roccodm/undeRaspWater/Images/board/IMG_20170130_133051.jpg

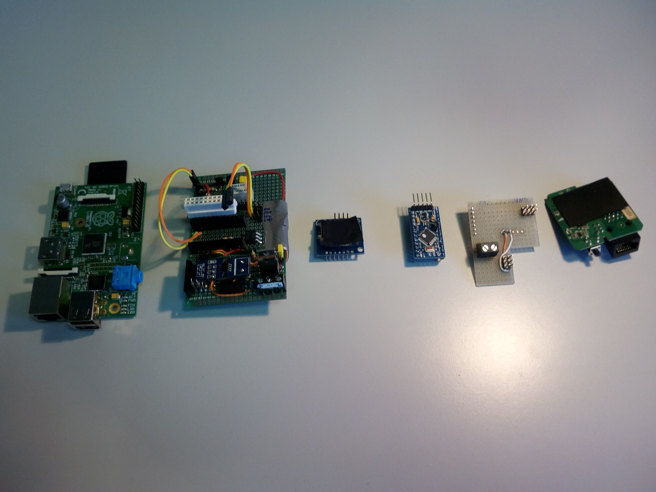
Images/board/IMG_20170130_133051.jpg
