roccodm/undeRaspWater/Images/board/IMG_20170130_133103.jpg

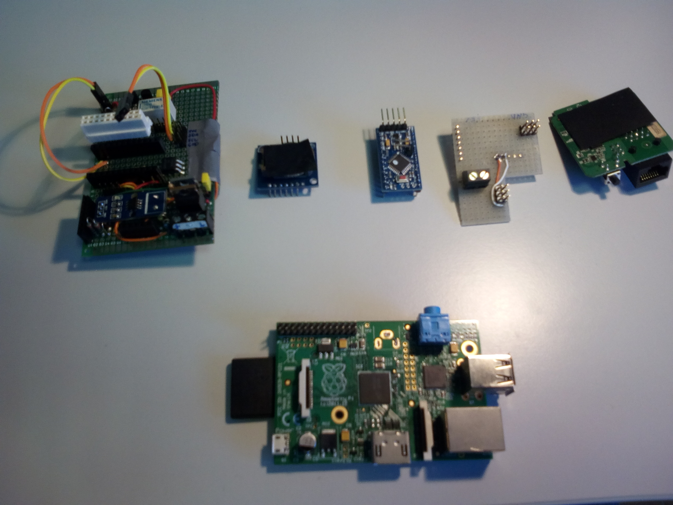
Images/board/IMG_20170130_133103.jpg
