roccodm/undeRaspWater/Images/board/IMG_20170130_133119.jpg

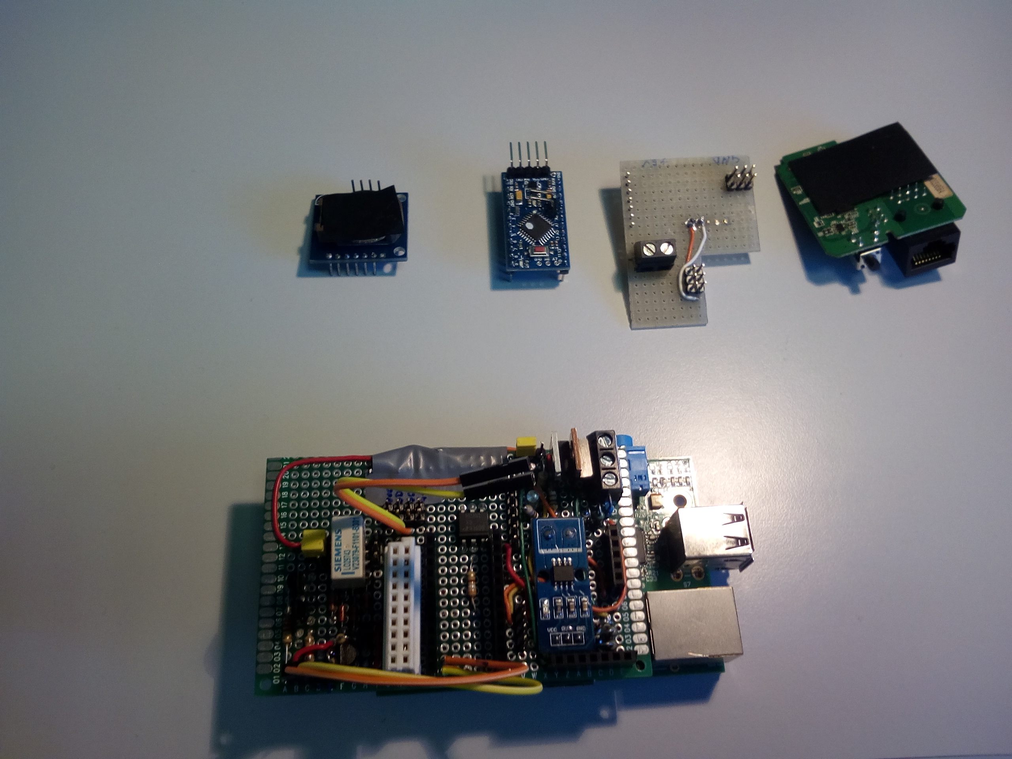
Images/board/IMG_20170130_133119.jpg
