roccodm/undeRaspWater/Images/board/IMG_20170130_133140.jpg

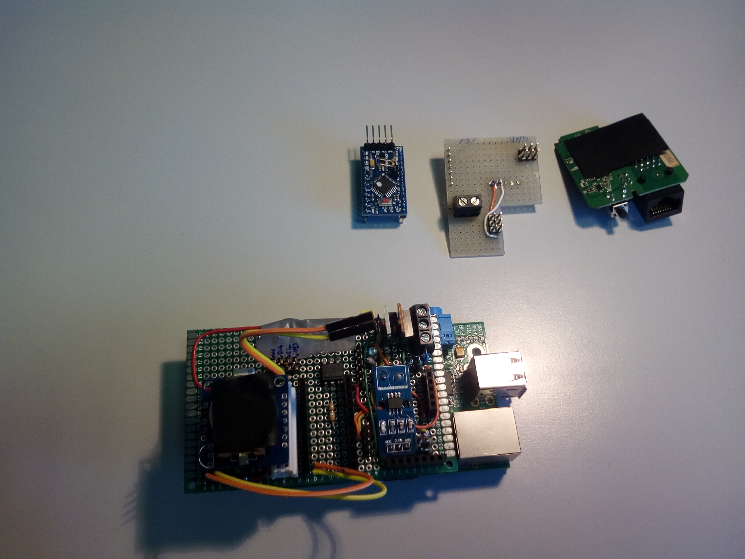
Images/board/IMG_20170130_133140.jpg
