roccodm/undeRaspWater/Images/board/IMG_20170130_133158.jpg

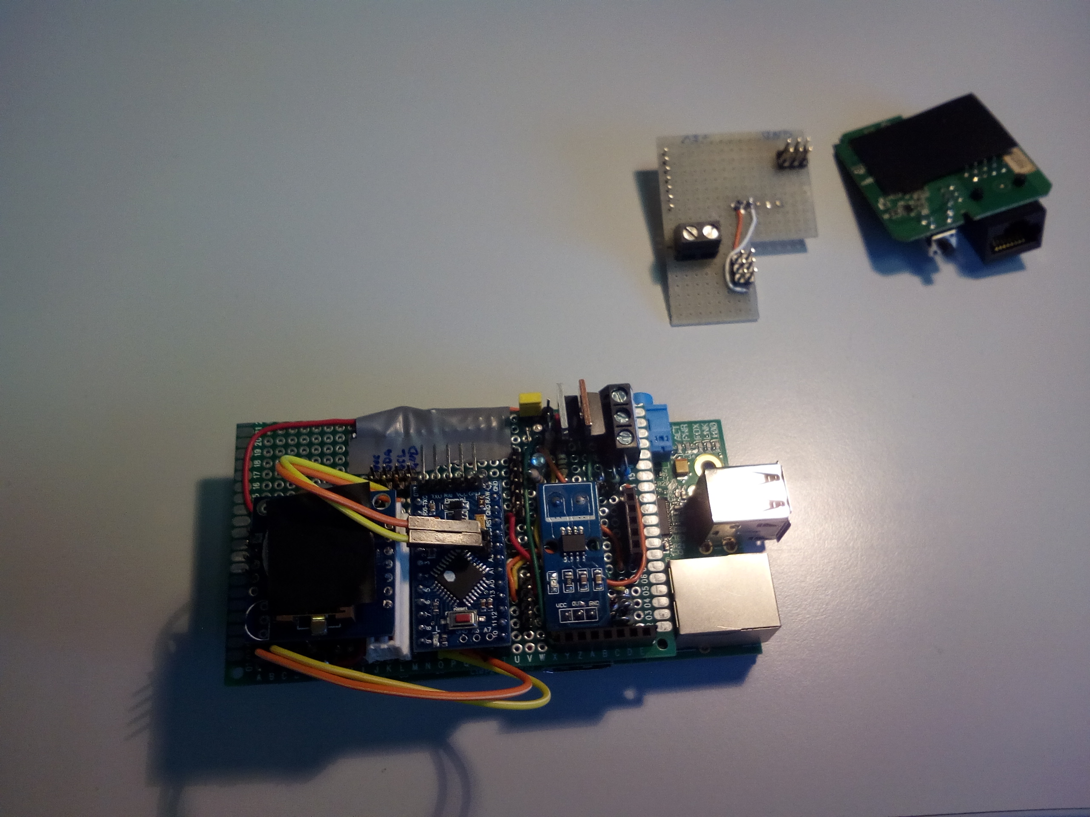
Images/board/IMG_20170130_133158.jpg
