roccodm/undeRaspWater/Images/board/IMG_20170130_133218.jpg

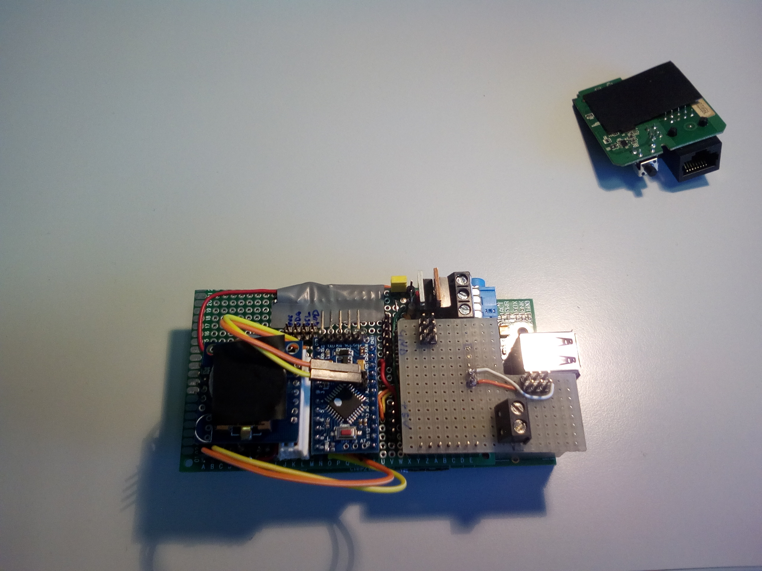
Images/board/IMG_20170130_133218.jpg
