roccodm/undeRaspWater/Images/board/IMG_20170130_133238.jpg

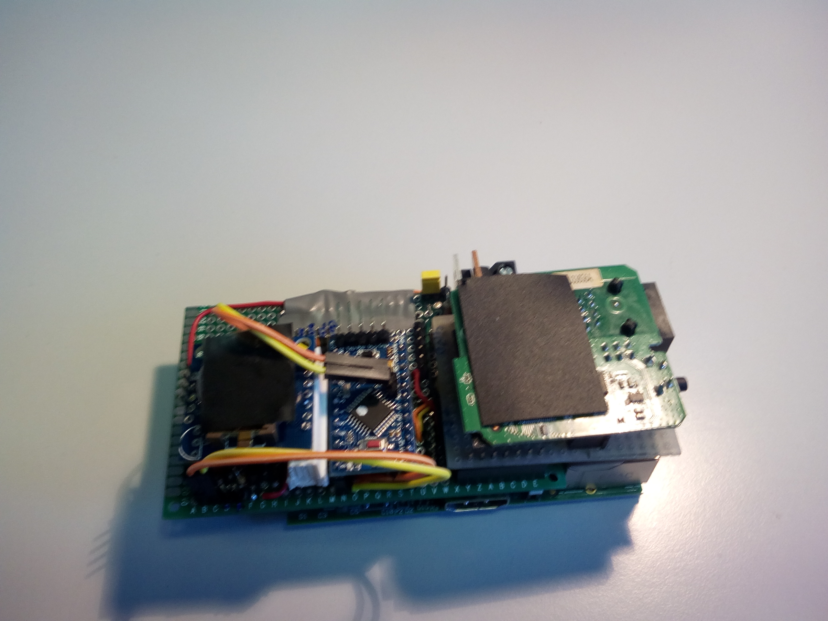
Images/board/IMG_20170130_133238.jpg
