roccodm/undeRaspWater/Images/board/IMG_20170130_133250.jpg

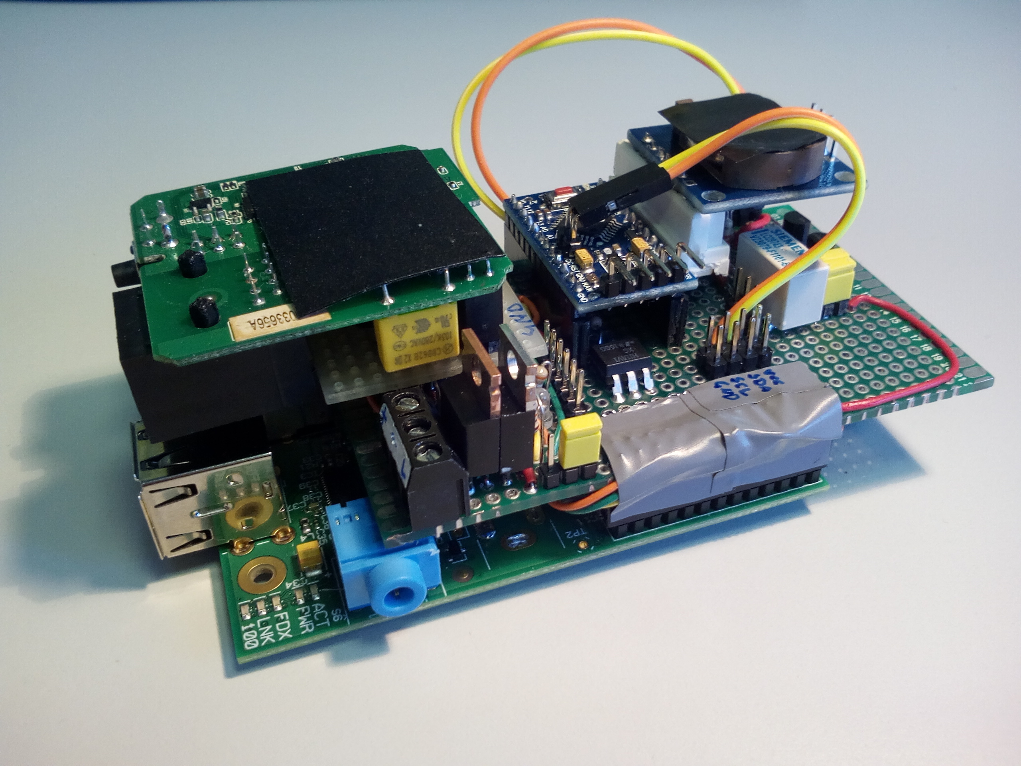
Images/board/IMG_20170130_133250.jpg
