roccodm/undeRaspWater/Images/board/IMG_20170202_100003.jpg

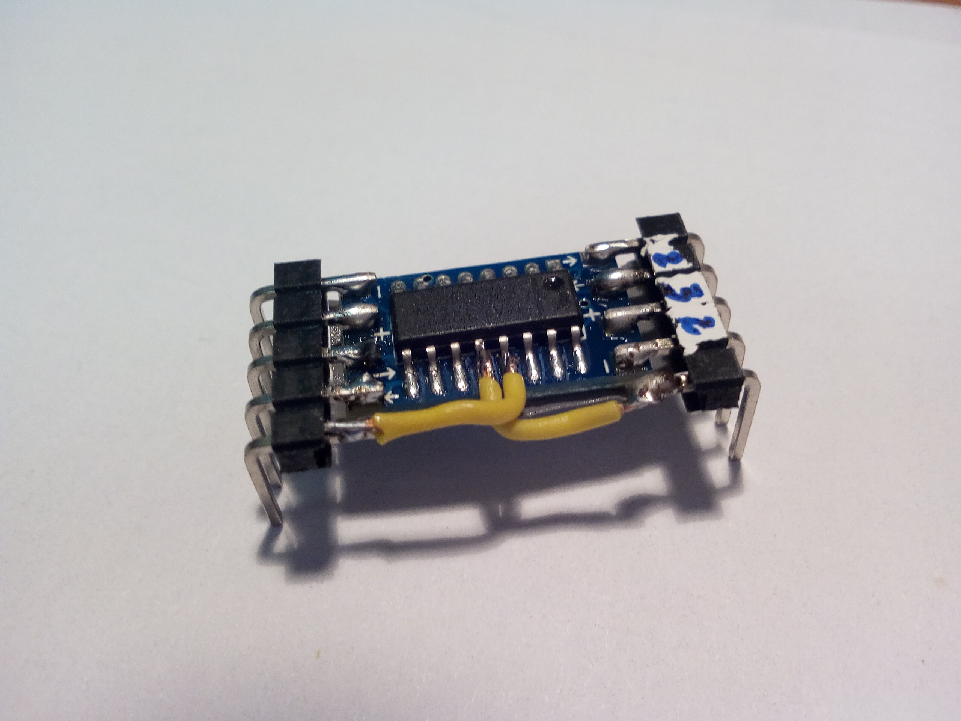
Images/board/IMG_20170202_100003.jpg
