roccodm/undeRaspWater/Images/board/IMG_20170202_102142.jpg

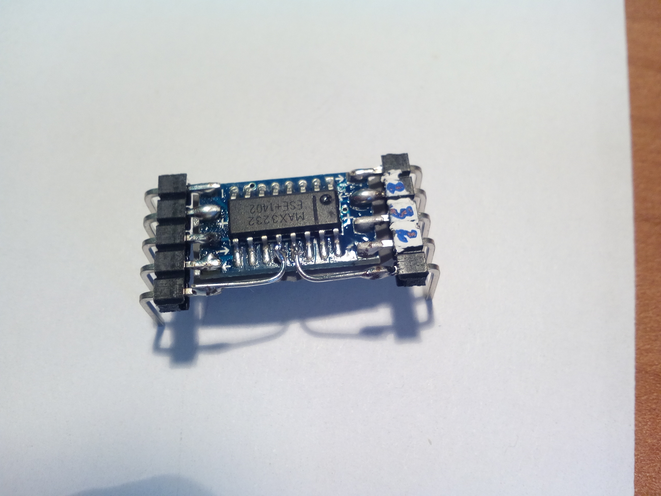
Images/board/IMG_20170202_102142.jpg
