roccodm/undeRaspWater/Images/board/IMG_20170202_103730.jpg

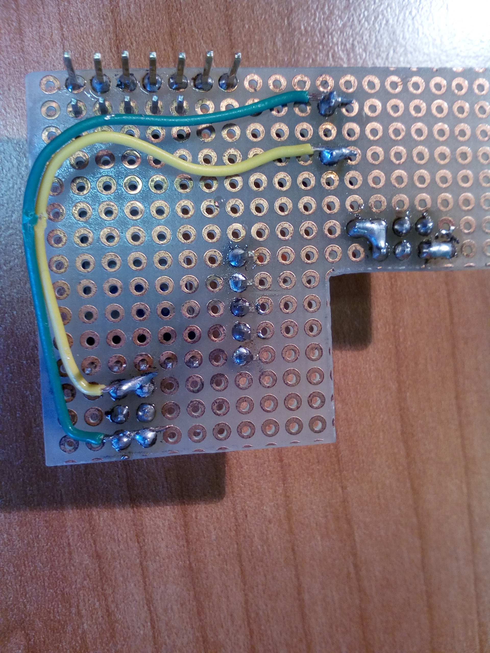
Images/board/IMG_20170202_103730.jpg
