roccodm/undeRaspWater/Images/board/IMG_20170202_123904.jpg

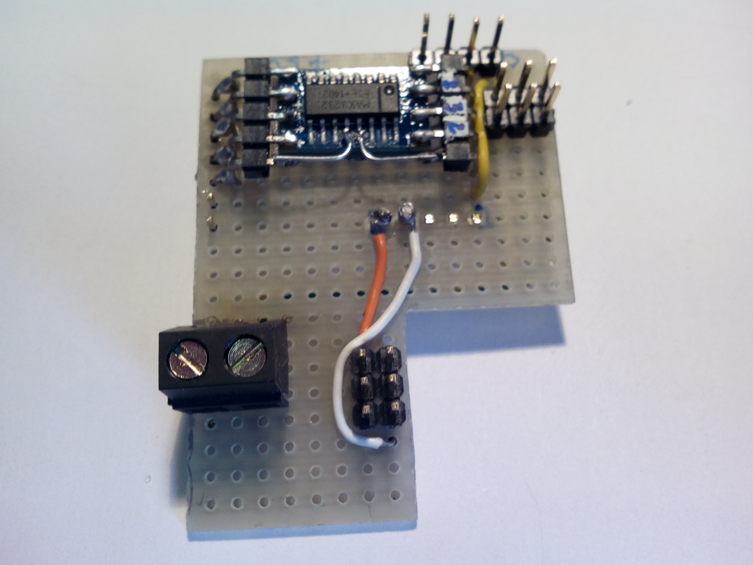
Images/board/IMG_20170202_123904.jpg
