roccodm/undeRaspWater/Images/board/IMG_20170202_125238.jpg

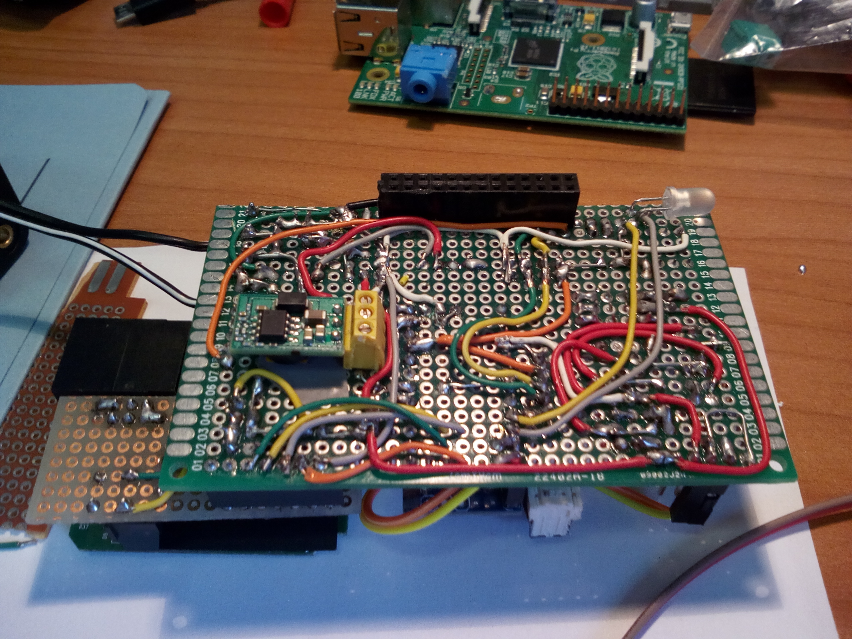
Images/board/IMG_20170202_125238.jpg
