roccodm/undeRaspWater/Images/board/IMG_20170202_125248.jpg

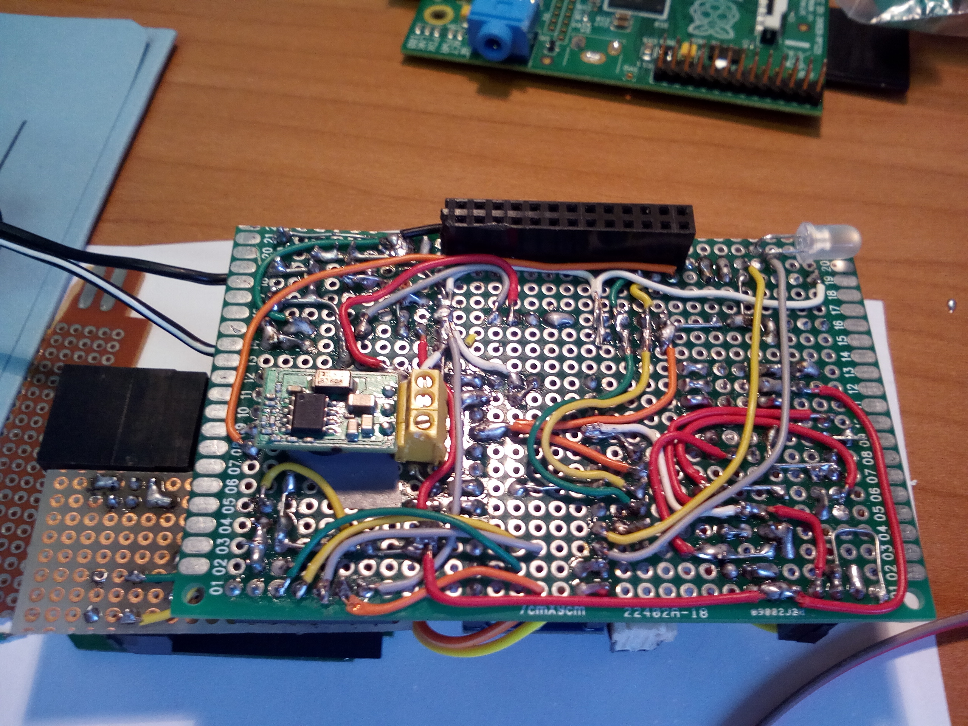
Images/board/IMG_20170202_125248.jpg
