roccodm/undeRaspWater/Images/board/IMG_20170202_141850.jpg

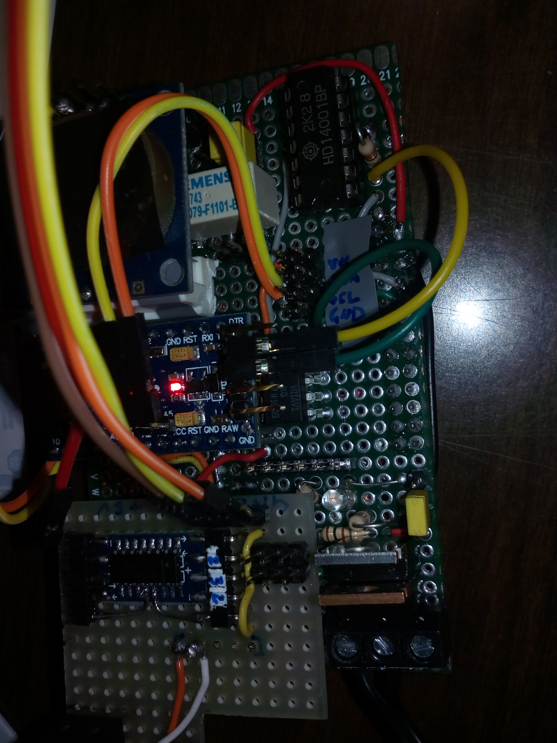
Images/board/IMG_20170202_141850.jpg
