roccodm/undeRaspWater/Images/board/IMG_20170203_102233.jpg

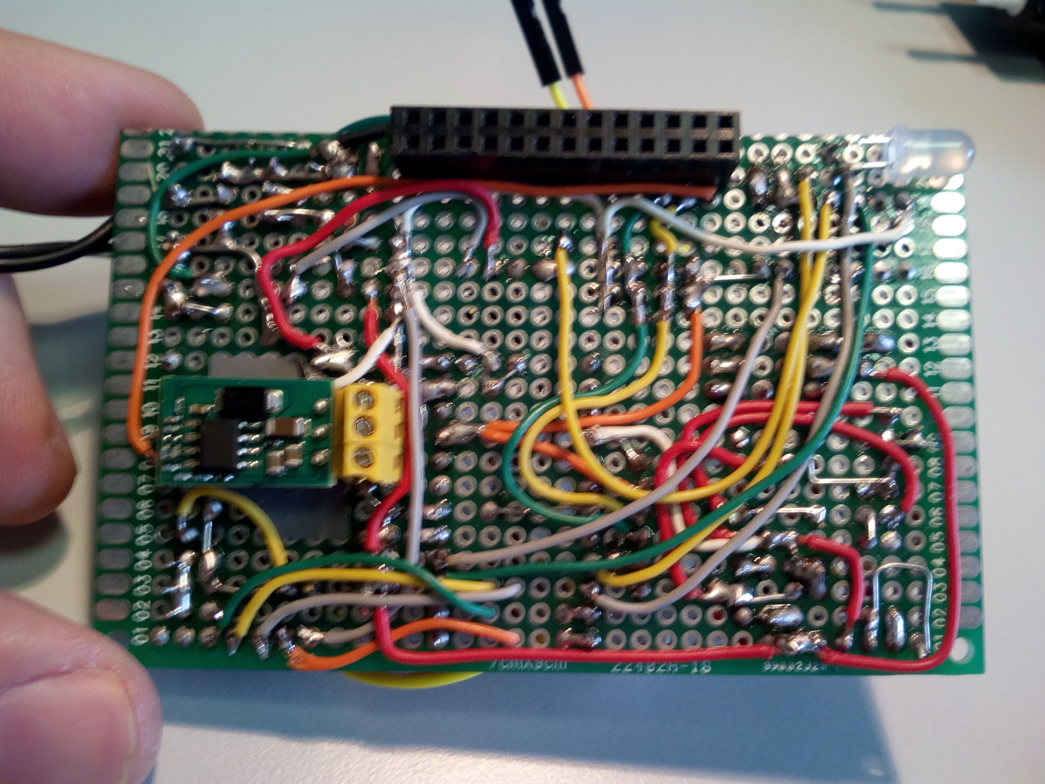
Images/board/IMG_20170203_102233.jpg
