roccodm/undeRaspWater/Images/board/IMG_20170203_102318.jpg

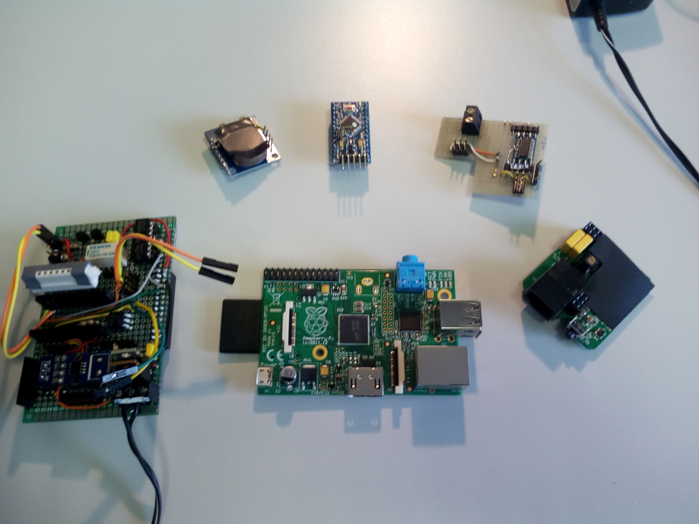
Images/board/IMG_20170203_102318.jpg
