roccodm/undeRaspWater/Images/board/IMG_20170203_102344.jpg

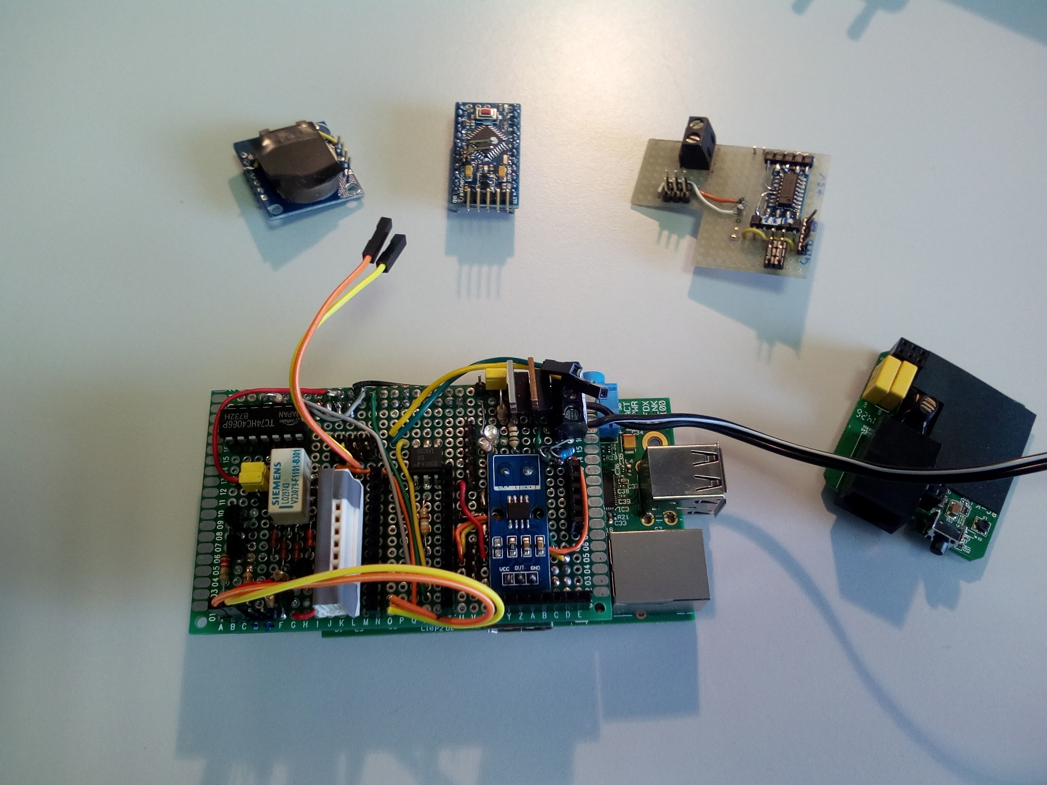
Images/board/IMG_20170203_102344.jpg
