roccodm/undeRaspWater/Images/board/IMG_20170203_102418.jpg

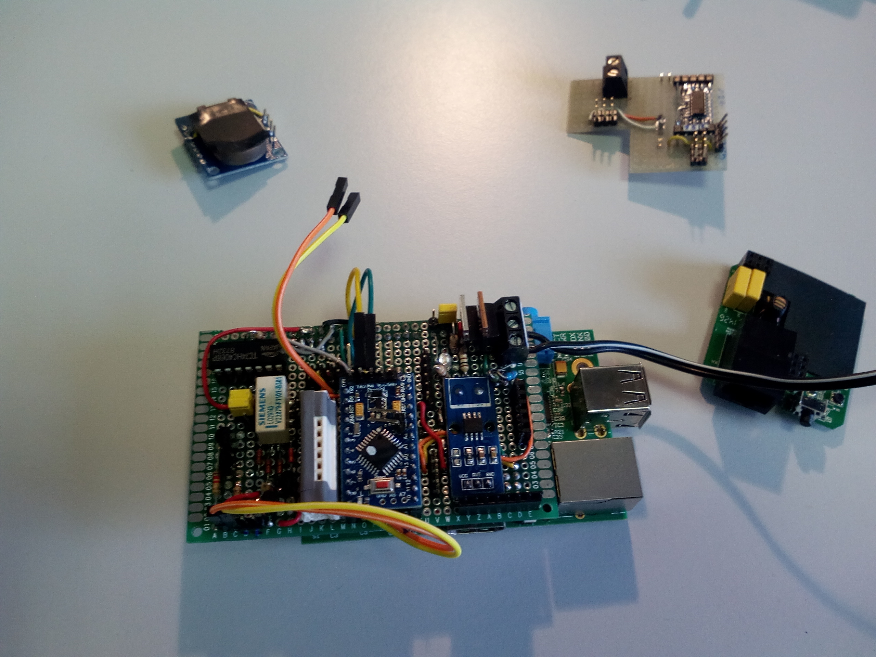
Images/board/IMG_20170203_102418.jpg
