roccodm/undeRaspWater/Images/board/IMG_20170203_102442.jpg

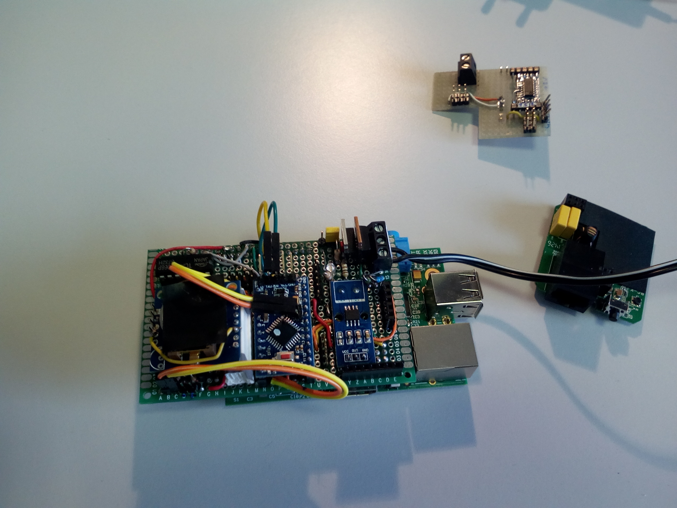
Images/board/IMG_20170203_102442.jpg
