roccodm/undeRaspWater/Images/board/IMG_20170203_102501.jpg

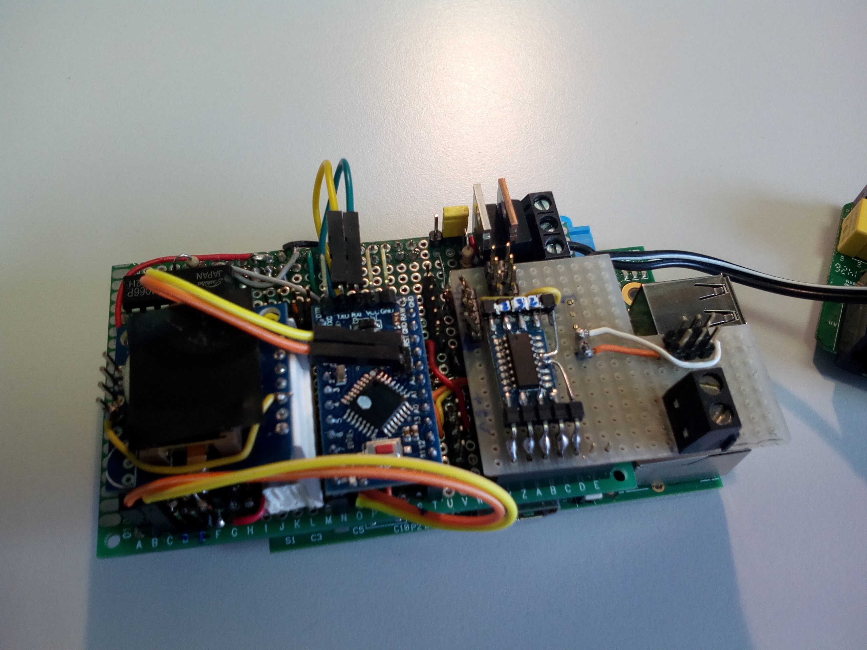
Images/board/IMG_20170203_102501.jpg
