roccodm/undeRaspWater/Images/board/IMG_20170203_102520.jpg

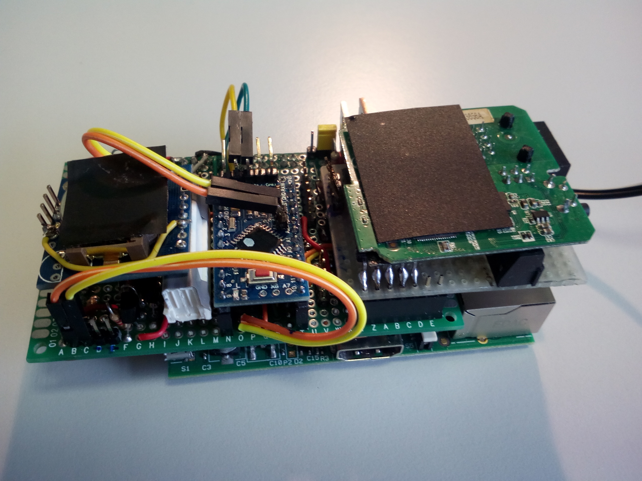
Images/board/IMG_20170203_102520.jpg
