roccodm/undeRaspWater/Images/board/IMG_20170203_102546.jpg

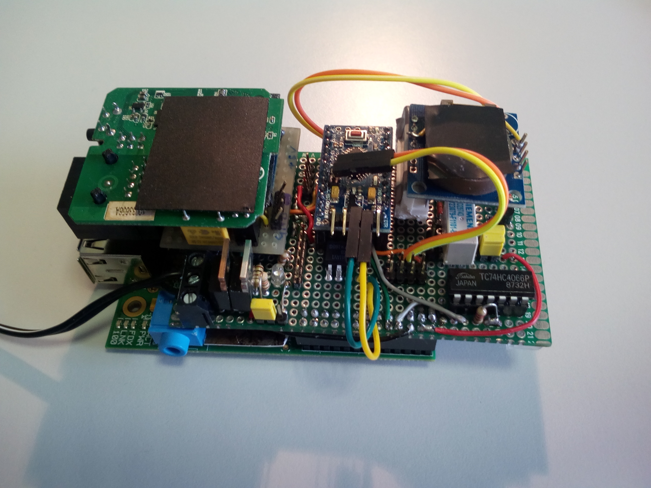
Images/board/IMG_20170203_102546.jpg
