roccodm/undeRaspWater/Images/board/IMG_20170207_112910.jpg

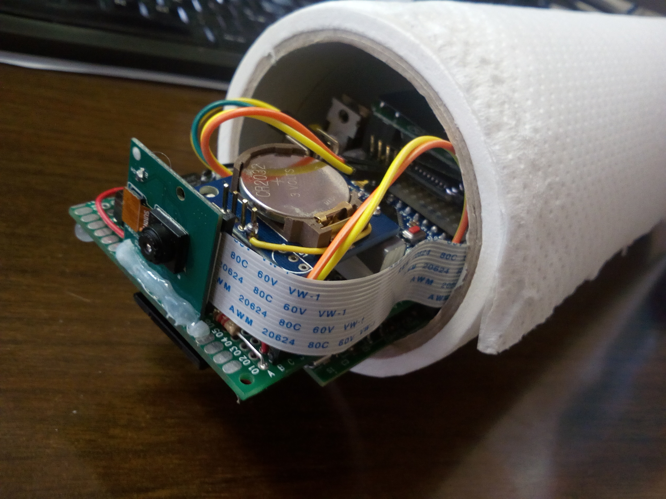
Images/board/IMG_20170207_112910.jpg
