roccodm/undeRaspWater/Images/board/IMG_20170316_121125.jpg

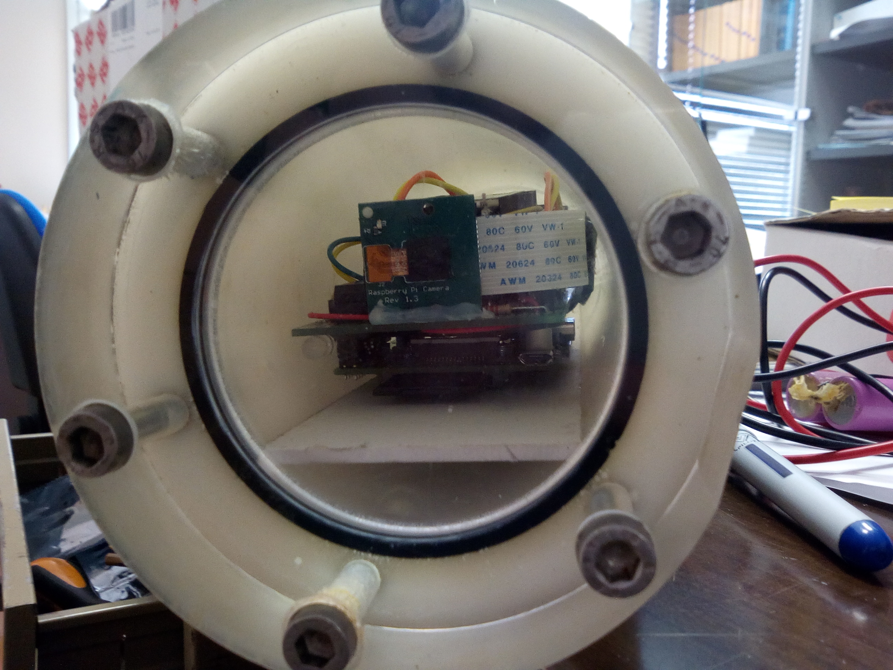
Images/board/IMG_20170316_121125.jpg
