roccodm/undeRaspWater/undeRaspino/undeRasp_v2a/rpi.h

#ifndef RPI_H
#define RPI_H

#include "defines.h"

// TIMERS
#define RPI_START_COOLDOWN 150
#define RPI_STOP_COOLDOWN 40
#define RPI_HEARTBEAT_RESET_TIME 20

// Setup
void rpi_setup();

// Run mode
uint8_t rpi_set_run_mode_s(char *in, char *err);
uint8_t rpi_get_run_mode();

// Status
int rpi_get_cooldown();
bool rpi_get_status();
bool rpi_has_power();
void rpi_set_halting(bool enabled);
void rpi_set_booted();
int rpi_set_checks_result(char *in, char *err);
int rpi_get_checks_result();

// Operations
void rpi_handle_ops();
void rpi_timers_update();
void rpi_start();
void rpi_stop();

// Start timer
void rpi_update_waketime();
int32_t rpi_get_restart_time_left();

// Manual mode
void rpi_set_manual(bool on);
bool rpi_is_manual();

// Serial status
void rpi_set_serial(bool enabled);

#endif
