roccodm/undeRaspWater/raspberry_side/home_pi/run.manual.py

#!/usr/bin/python -u
# -*- coding: utf-8 -*-
##################################################
# run.manual.py
##################################################
import time


while True:
   time.sleep(1)
